ts-manuel/VideoFrame/stm32/Core/Inc/sd_driver.h

/**
 ******************************************************************************
 * @file      sd_driver.h
 * @author    ts-manuel
 * @brief     Driver for the SD-Card
 *
 ******************************************************************************
 */

#ifndef INC_SD_DRIVER_H_
#define INC_SD_DRIVER_H_

#include <stdint.h>
#include <stdbool.h>
#include "fatfs.h"
#include "stm32f4xx_hal.h"
#include "power.h"


HAL_StatusTypeDef SD_Init(SD_HandleTypeDef* hsd, FATFS* fs);
HAL_StatusTypeDef SD_Sleep(SD_HandleTypeDef* hsd);

#endif /* INC_SD_DRIVER_H_ */
