ts-manuel/VideoFrame/stm32/Core/Inc/display_driver.h

/**
 ******************************************************************************
 * @file      display_driver.h
 * @author    ts-manuel
 * @brief     Driver for the E-Paper display
 *
 ******************************************************************************
 */

#ifndef INC_DISPLAY_DRIVER_H_
#define INC_DISPLAY_DRIVER_H_

#include <stdint.h>
#include <stdbool.h>
#include "EPD_5in65f.h"

#define _DITHER 1			//0 = no dither, 1 = Floyd–Steinberg
#define _VCOM_MV	1050	//VCOM Voltage mV (the proper voltage for the panel is written on the flex cable)

void DISP_Init(void);
void DISP_Sleep(void);
void DISP_BeginUpdate(void);
void DISP_EndUpdate(void);
void DISP_Clear(uint8_t color);
void DISP_ShowBlocks(void);
void DISP_ShowStripes(void);
void DISP_ShowLines(void);
void DISP_ShowGradient(uint8_t color);
void DISP_SetStripeHeight(int h);
void DISP_WritePixel(int x, int y, uint8_t r, uint8_t g, uint8_t b);

#endif /* INC_DISPLAY_DRIVER_H_ */
